Yurisu/meshtastic-faketecyuri/image/20250114_002313.JPG

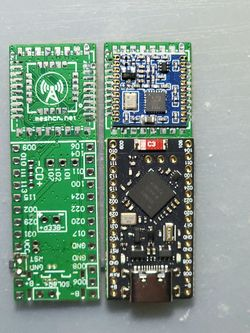
image/20250114_002313.JPG
