Yurisu/meshtastic-faketecyuri/image/20250114_010101.JPG

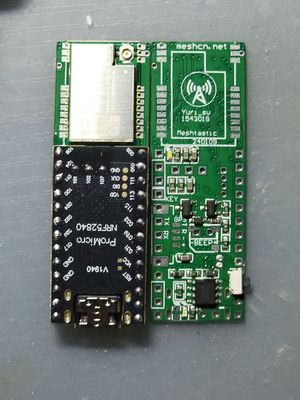
image/20250114_010101.JPG
