Yurisu/meshtastic-faketecyuri/image/20250114_010630.JPG

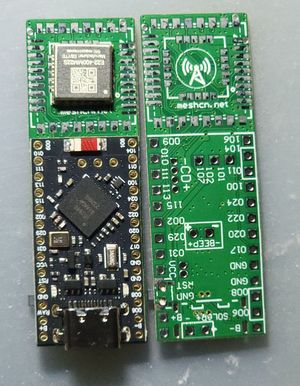
image/20250114_010630.JPG
