Yurisu/meshtastic-faketecyuri/image/20250721210935.jpg

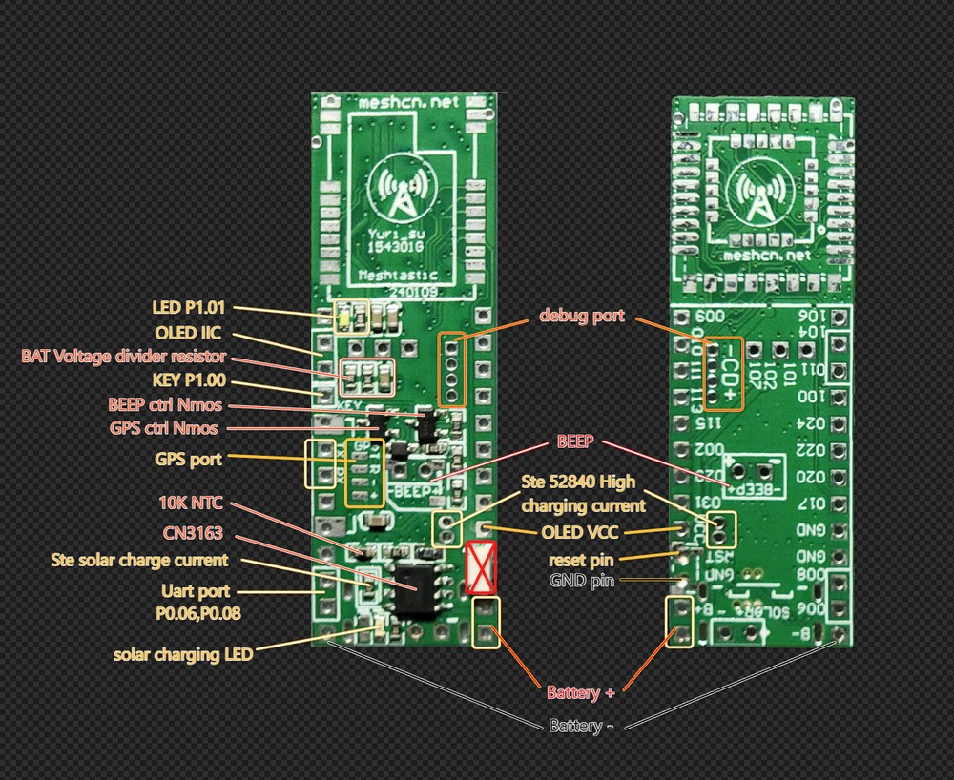
image/20250721210935.jpg
